pfory/humidity-sensor/pict/net01.PNG

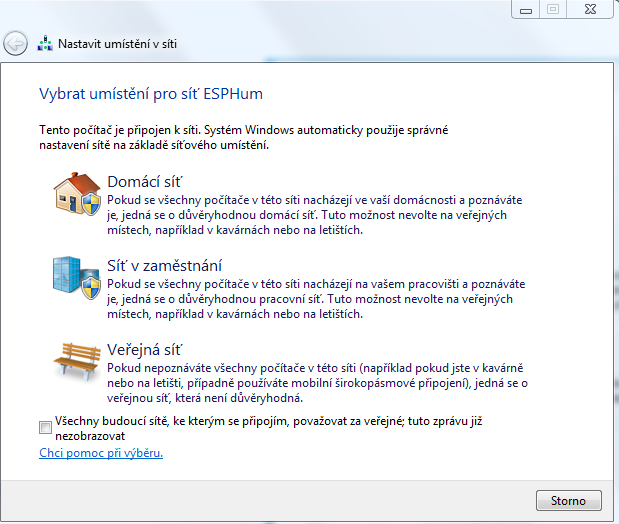
pict/net01.PNG
