pfory/humidity-sensor/pict/xivelyApi.PNG

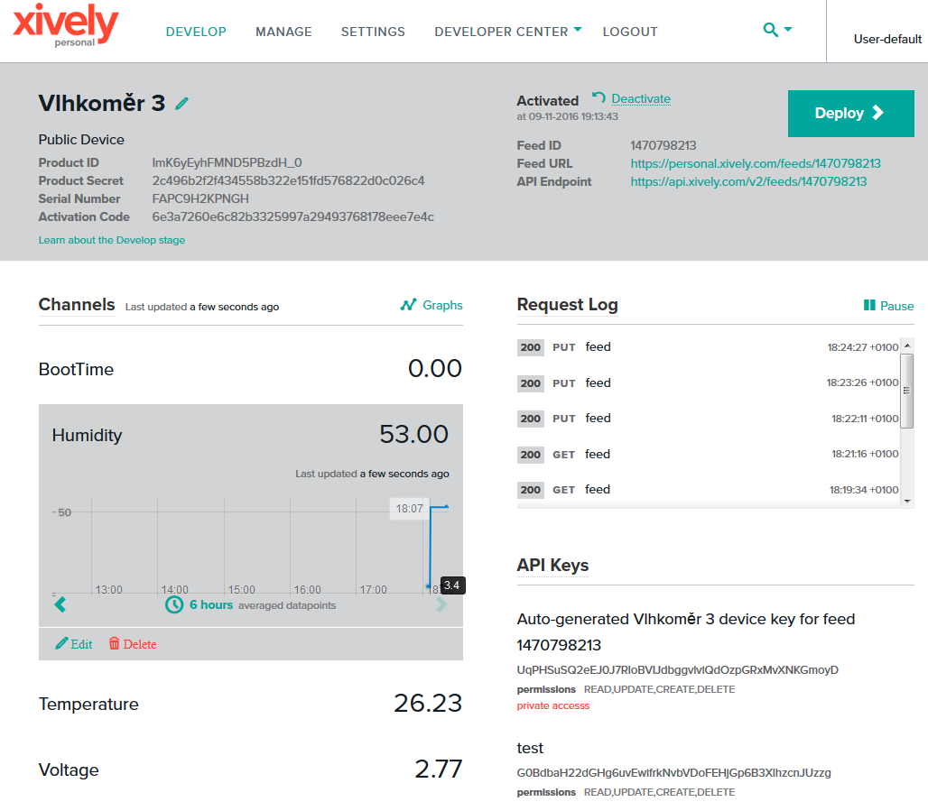
pict/xivelyApi.PNG
