pfory/humidity-sensor/test.lua

-- MQTT connect script with deep sleep
-- Remember to connect GPIO16 and RST to enable deep sleep

--############
--# Settings #
--############

--- MQTT ---
mqtt_broker_ip = "88.146.202.186"     
mqtt_broker_port = 31883
mqtt_username = "datel"
mqtt_password = "hanka12"
mqtt_client_id = ""

--- WIFI ---
wifi_SSID = "Datlovo"
wifi_password = "Nu6kMABmseYwbCoJ7LyG"
-- wifi.PHYMODE_B 802.11b, More range, Low Transfer rate, More current draw
-- wifi.PHYMODE_G 802.11g, Medium range, Medium transfer rate, Medium current draw
-- wifi.PHYMODE_N 802.11n, Least range, Fast transfer rate, Least current draw 
wifi_signal_mode = wifi.PHYMODE_N
-- If the settings below are filled out then the module connects 
-- using a static ip address which is faster than DHCP and 
-- better for battery life. Blank "" will use DHCP.
-- My own tests show around 1-2 seconds with static ip
-- and 4+ seconds for DHCP
client_ip=""
client_netmask=""
client_gateway=""

--- INTERVAL ---
-- In milliseconds. Remember that the sensor reading, 
-- reboot and wifi reconnect takes a few seconds
time_between_sensor_readings = 60000

--################
--# END settings #
--################

-- Setup MQTT client and events
m = mqtt.Client(client_id, 120, username, password)
temperature = 100
humidity = 500

-- Connect to the wifi network
wifi.setmode(wifi.STATION) 
wifi.setphymode(wifi_signal_mode)
wifi.sta.config(wifi_SSID, wifi_password) 
wifi.sta.connect()
if client_ip ~= "" then
    wifi.sta.setip({ip=client_ip,netmask=client_netmask,gateway=client_gateway})
end

-- DHT22 sensor logic
function get_sensor_Data() 
  
end

function loop() 
    if wifi.sta.status() == 5 then
        -- Stop the loop
        tmr.stop(0)
        m:connect( mqtt_broker_ip , mqtt_broker_port, 0, function(conn)
            print("Connected to MQTT")
            print("  IP: ".. mqtt_broker_ip)
            print("  Port: ".. mqtt_broker_port)
            print("  Client ID: ".. mqtt_client_id)
            print("  Username: ".. mqtt_username)
            -- Get sensor data
            get_sensor_Data() 
            m:publish("/home/sklenik/esp10/temperature",(temperature / 10).."."..(temperature % 10), 0, 0, function(conn)
                m:publish("/home/sklenik/esp10/humidity",(humidity / 10).."."..(humidity % 10), 0, 0, function(conn)
                    print("Going to deep sleep for "..(time_between_sensor_readings/1000).." seconds")
                    node.dsleep(time_between_sensor_readings*1000)             
                end)          
            end)
        end )
    else
        print("Connecting...")
    end
end
        
tmr.alarm(0, 100, 1, function() loop() end)
